cheyao/aniboard/PCB/art/acon.png

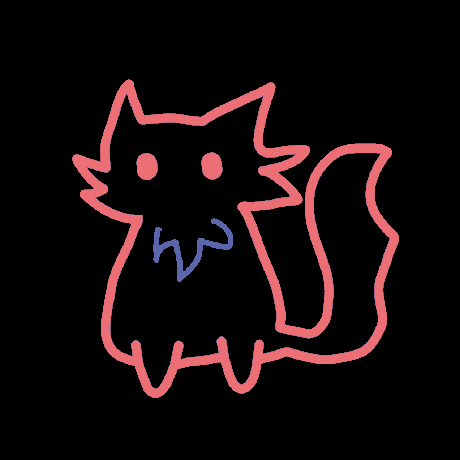
PCB/art/acon.png
