cheyao/aniboard/PCB/art/blah.png

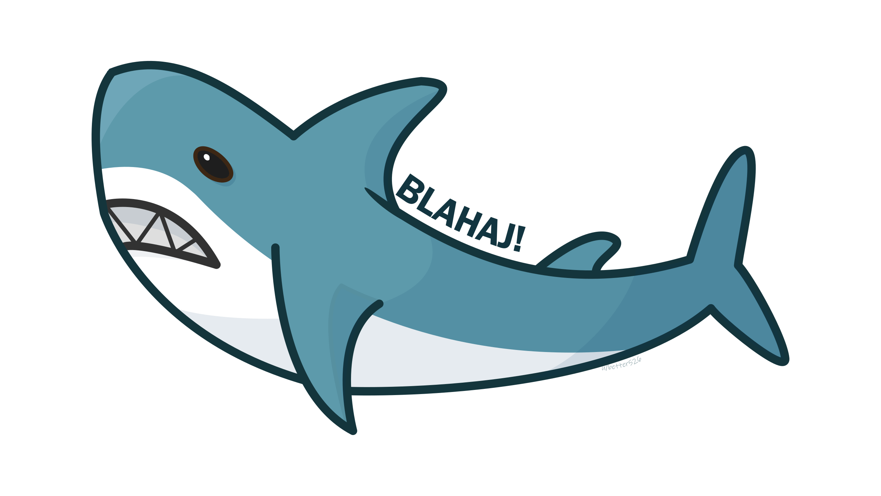
PCB/art/blah.png
