cheyao/aniboard/PCB/art/chisato-cute-shooting.jpg

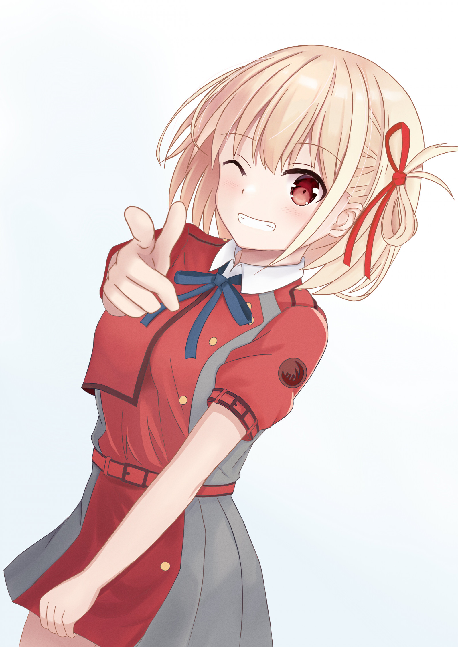
PCB/art/chisato-cute-shooting.jpg
