cheyao/aniboard/PCB/art/gura-a.png

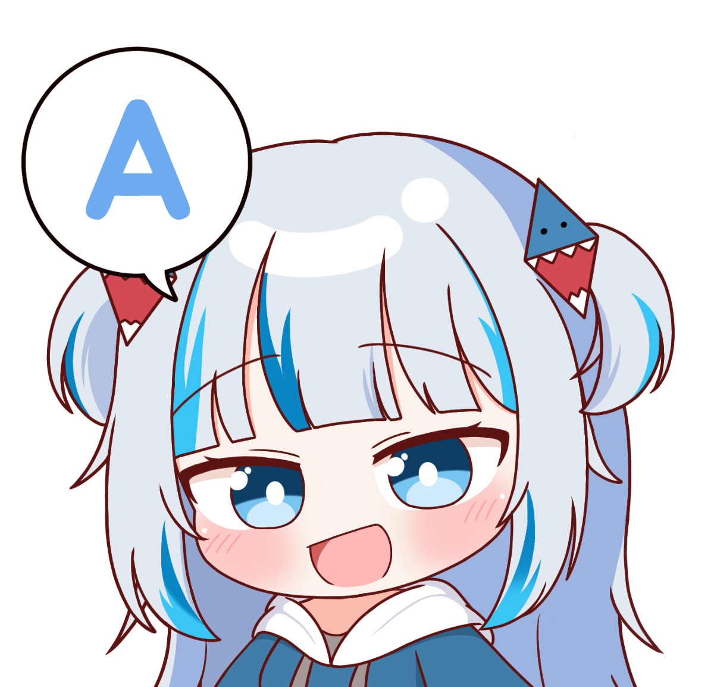
PCB/art/gura-a.png
