cheyao/aniboard/PCB/art/s.jpg

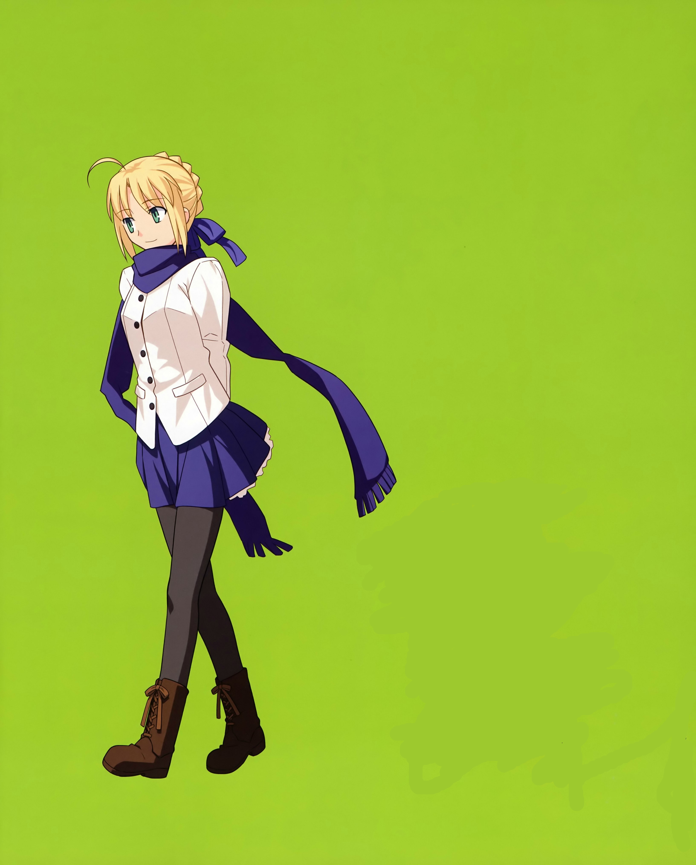
PCB/art/s.jpg
