cheyao/aniboard/PCB/art/saber-brage.jpg

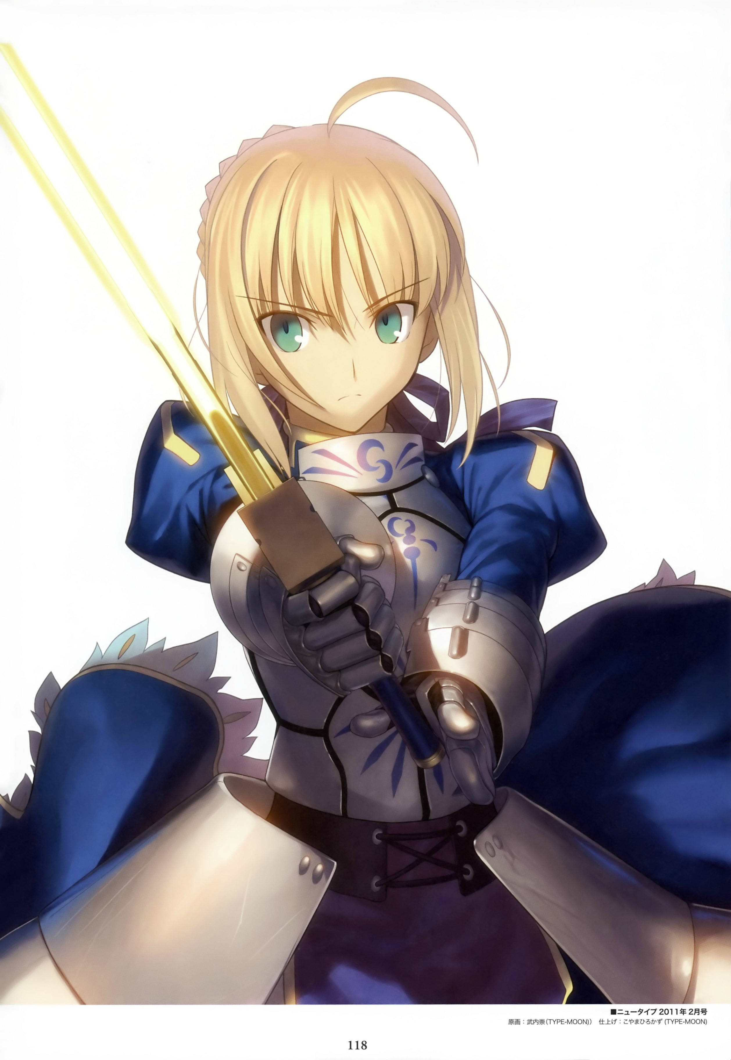
PCB/art/saber-brage.jpg
