cheyao/aniboard/PCB/models/SW_Cherry_MX_PCB.stp

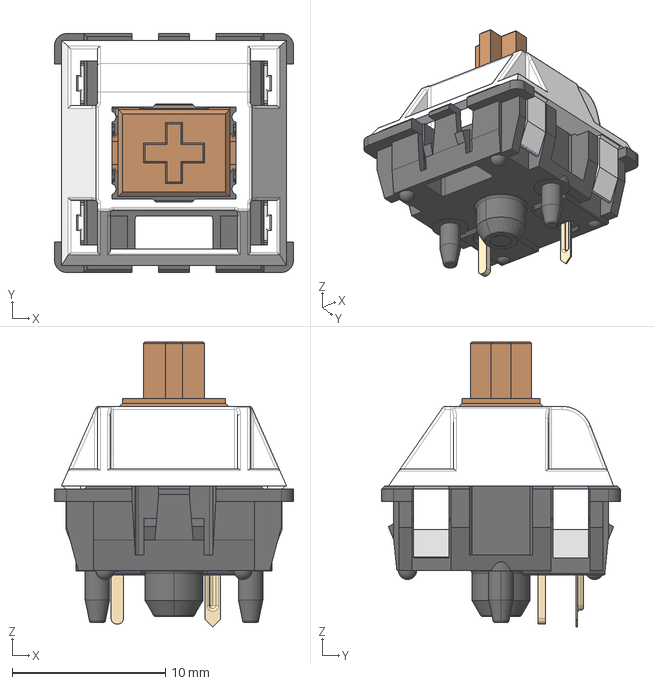
[picture p27: CAD file, 2025-02-11]
PCB/models/SW_Cherry_MX_PCB.stp
15.6 x 15.6 x 18.6 mm
