cheyao/aniboard/CAD/archive/assembly.stl

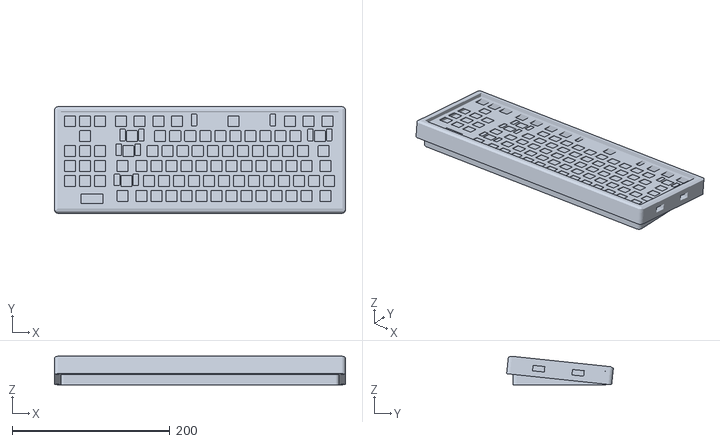
[picture p28: CAD file, 2025-03-05, an earlier design]
CAD/archive/assembly.stl
369.0 x 135.5 x 36.2
